theodornitu/blindaids/Images/CR2-3-6V-1000mAh-15266-Li-ion-Battery.jpg

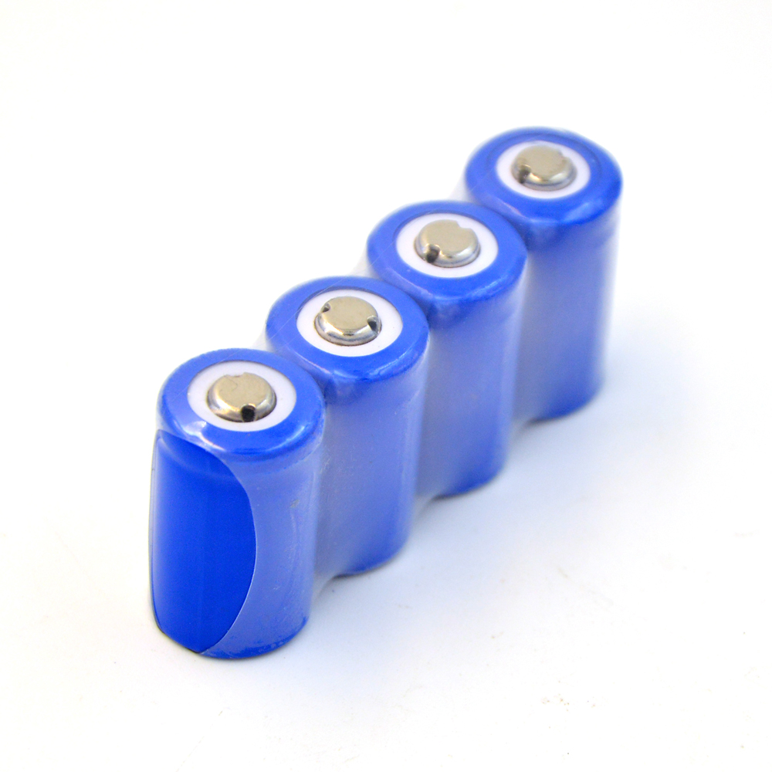
Images/CR2-3-6V-1000mAh-15266-Li-ion-Battery.jpg
